TinyCircuits/TinyCircuits-TinyShield-Circle_Leds-ASD2412/images/ASD2412-R-LG-Tutorial-Image-03.jpg

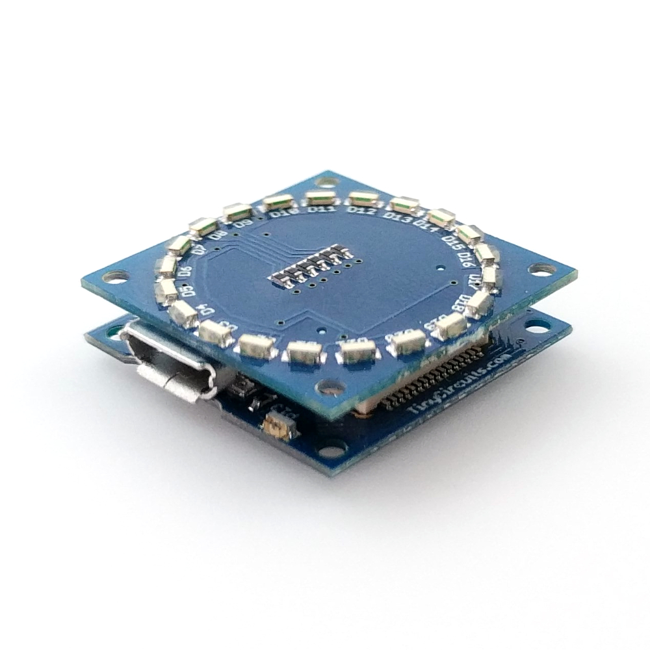
images/ASD2412-R-LG-Tutorial-Image-03.jpg
